besi/split-flap-clock/dxf/v1/2mm-makercase-outer-40-4--80-9--45-58.dxf

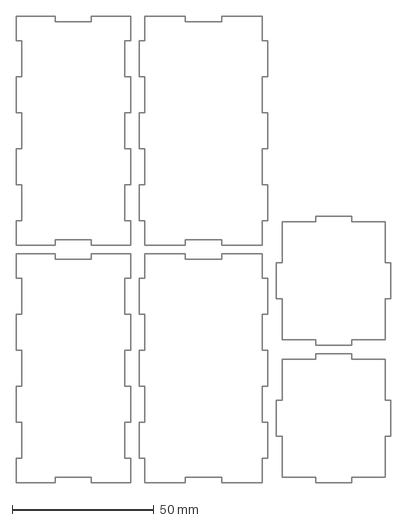
[picture p26: CAD file, 2025-01-19, an earlier design]
dxf/v1/2mm-makercase-outer-40-4--80-9--45-58.dxf
132.4 x 164.8 mm
